qiaoyo/TellMeLight/hardware/outputs/rev_a1/tellmelight_rev_a1_bottom.png

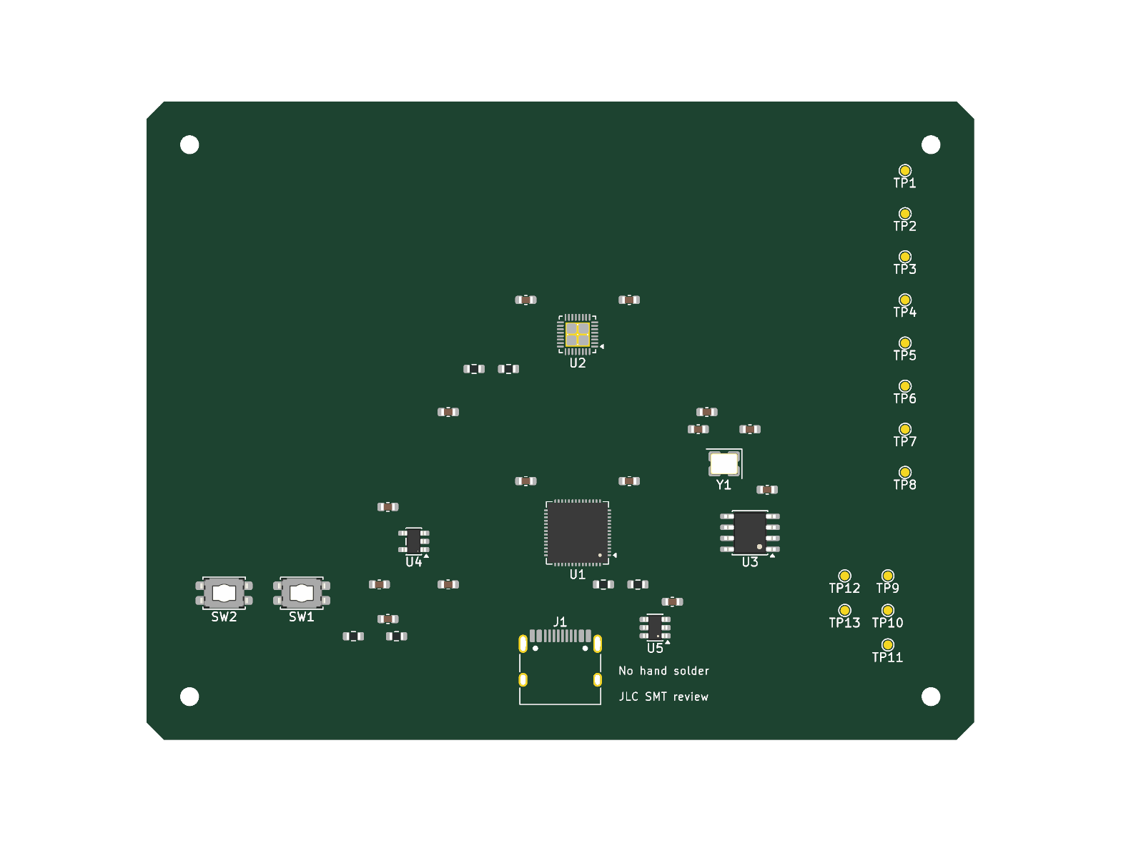
hardware/outputs/rev_a1/tellmelight_rev_a1_bottom.png
