qiaoyo/TellMeLight/hardware/outputs/rev_a1/tellmelight_rev_a1_top.png

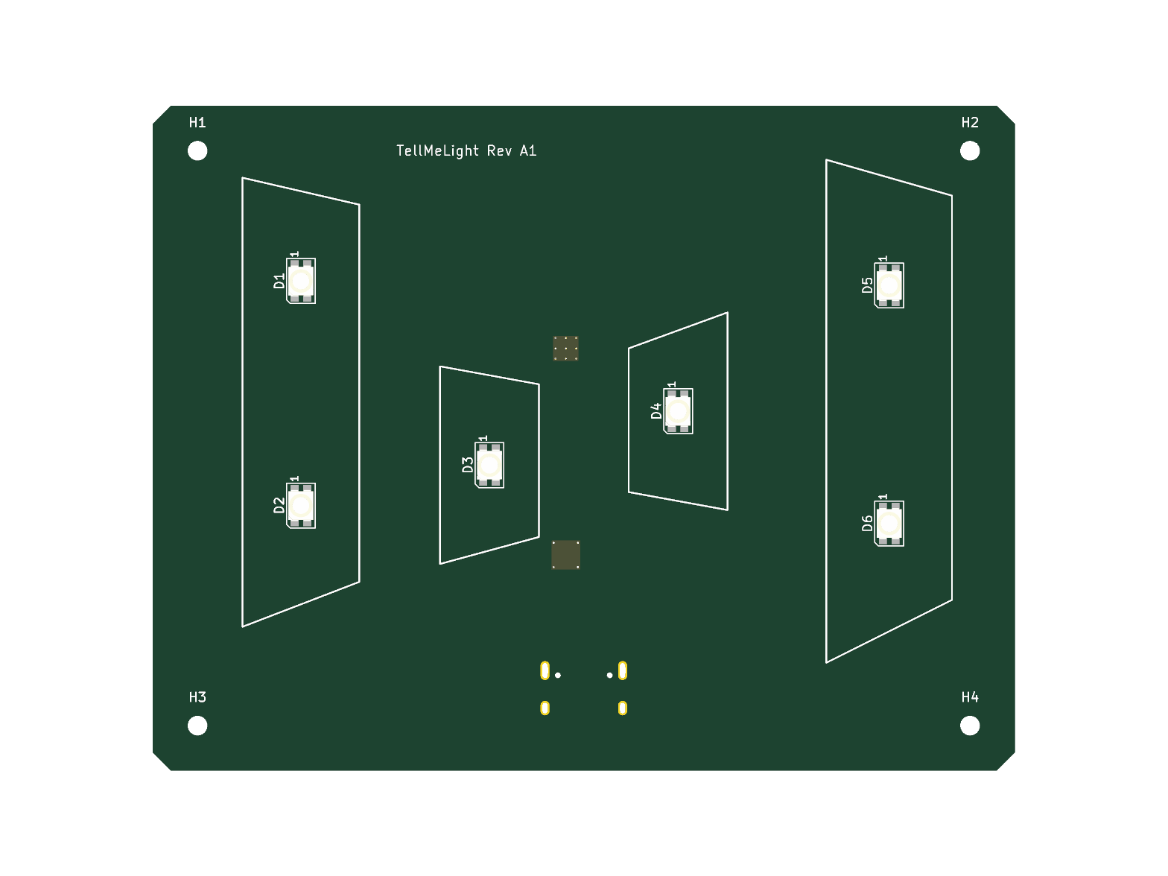
hardware/outputs/rev_a1/tellmelight_rev_a1_top.png
